AdilSevim/Custom-Iris-Diaphragm/docs/image1.png

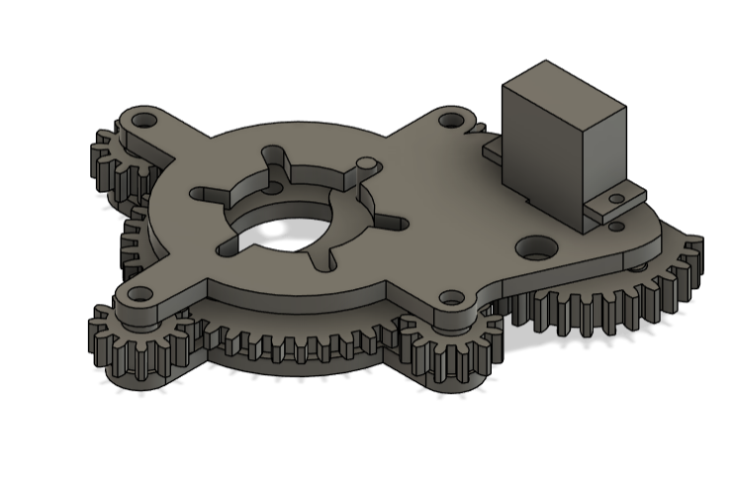
docs/image1.png
