AdilSevim/Custom-Iris-Diaphragm/docs/image2.png

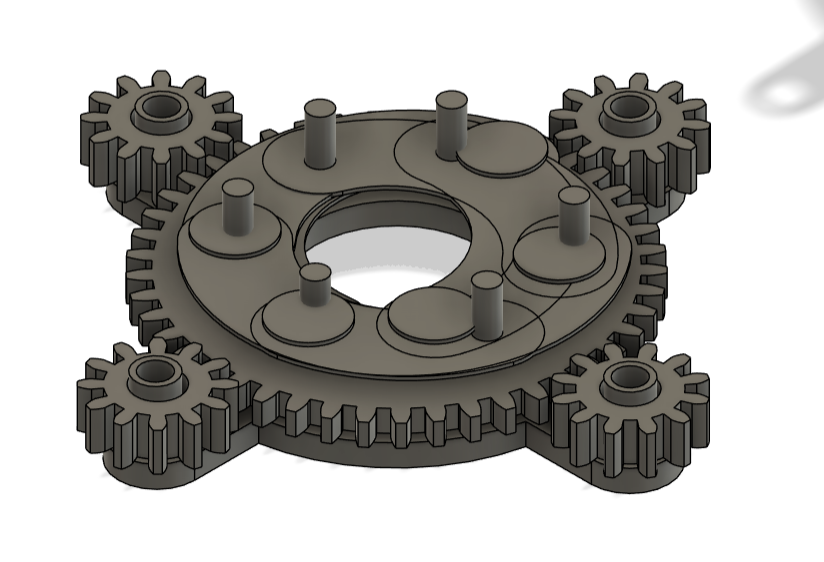
docs/image2.png
