AdilSevim/Custom-Iris-Diaphragm/docs/image4.png

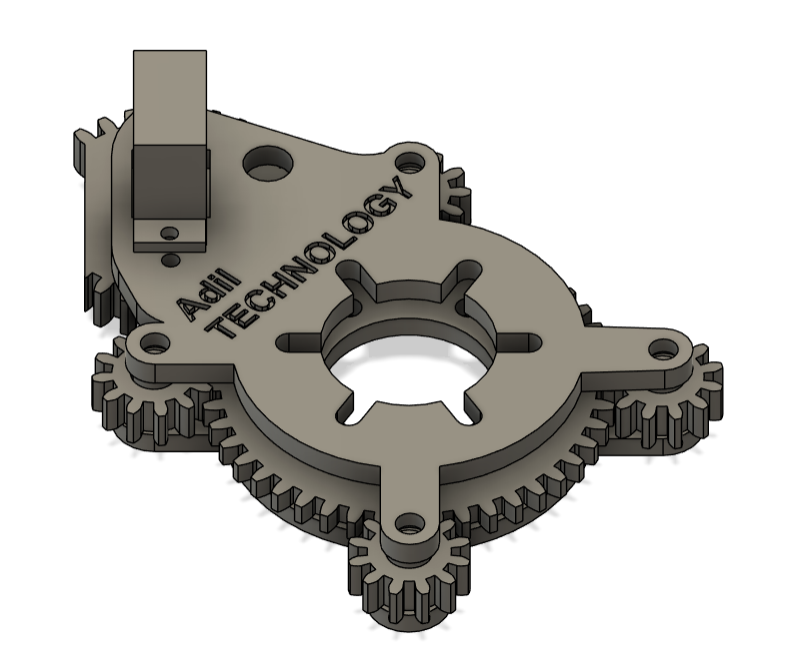
docs/image4.png
