AdilSevim/Custom-Iris-Diaphragm/docs/image5.png

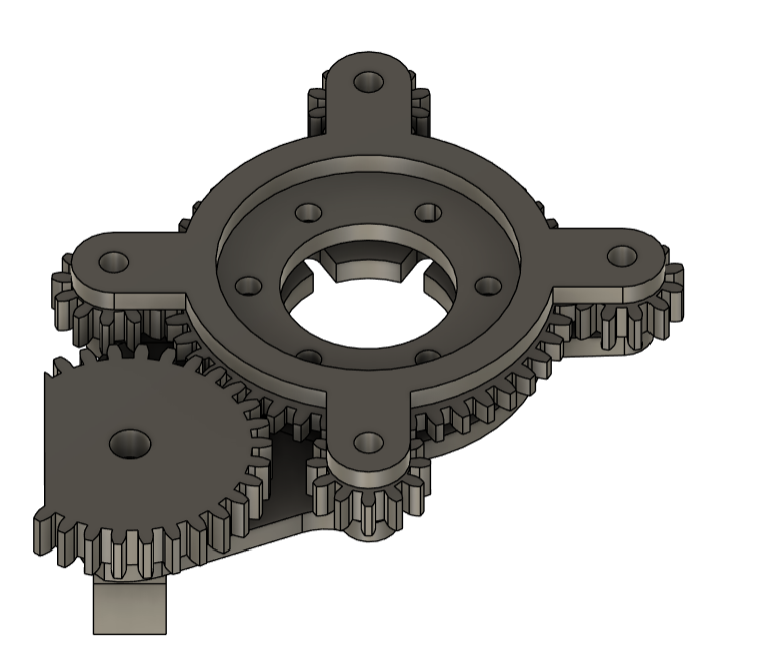
docs/image5.png
