AdilSevim/Custom-Iris-Diaphragm/docs/image7.png

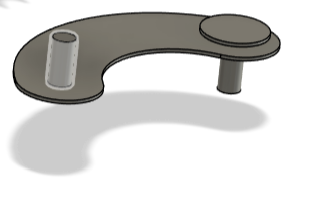
docs/image7.png
